dovker/Touchord/img/DSC_5180.jpg

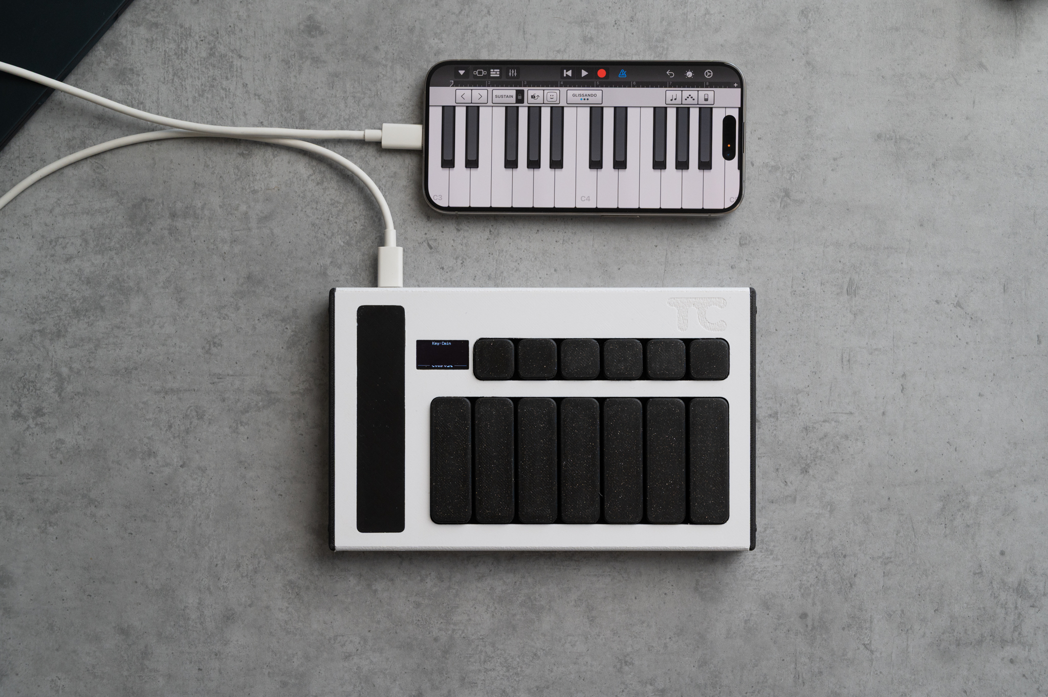
img/DSC_5180.jpg
