dovker/Touchord/img/DSC_5195.jpg

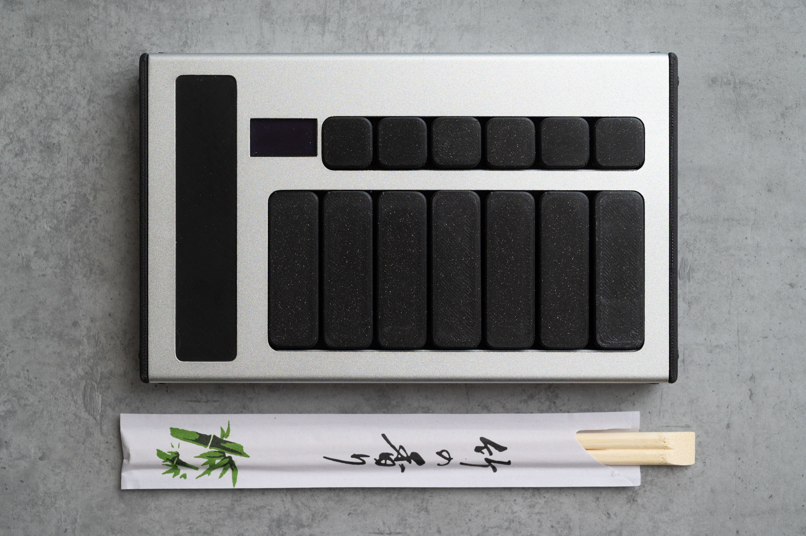
img/DSC_5195.jpg
