dovker/Touchord/src/IO/Midi.c

/*
 * Touchord — MIDI chord controller firmware.
 * Copyright (C) 2025-2026 MB Daugdara
 * SPDX-License-Identifier: GPL-3.0-or-later
 *
 * For more info, email info@daugdara.com
 */

#include "Midi.h"
#include "tusb.h"
#include "hardware/uart.h"

void switch_midi_trs(MidiType type)
{
    //Toggles the TS5A23157DGSR
    switch(type)
    {
        case MIDI_TRS_A:
        gpio_put(MIDI_PIN_IN_1, 0);
        gpio_put(MIDI_PIN_IN_2, 0);
        break;
        case MIDI_TRS_B:
        gpio_put(MIDI_PIN_IN_1, 1);
        gpio_put(MIDI_PIN_IN_2, 1);
        break;
    }
}
void setup_midi_trs(MidiType type)
{
    gpio_init(MIDI_PIN_IN_1);
    gpio_init(MIDI_PIN_IN_2);
    gpio_set_dir(MIDI_PIN_IN_1, GPIO_OUT);
    gpio_set_dir(MIDI_PIN_IN_2, GPIO_OUT);

    switch_midi_trs(type);

    uart_init(uart1, MIDI_BAUD_RATE);
    gpio_set_function(MIDI_PIN_DAT, GPIO_FUNC_UART); //MIDI_PIN_DAT is TX pin
    uart_set_hw_flow(uart1, false, false);
    uart_set_format(uart1, 8, 1, UART_PARITY_NONE);
    uart_set_fifo_enabled(uart1, false);
}

void send_trs_midi(uint8_t* data, uint8_t len)
{
    for(int i = 0; i < len; i++)
    {
        uart_putc_raw(uart1, data[i]);
    }
}

void send_midi_chord(uint8_t channel, uint8_t status, uint8_t* notes, uint8_t length, uint8_t velocity)
{
    for(int i = 0; i < length; i++)
    {
        send_midi_note(channel, status, notes[i], velocity);
    }
}

void send_midi_chord_diff(const uint8_t *prev, const uint8_t *curr,
                          uint8_t channel, uint8_t velocity, bool retrigger)
{
    if (retrigger) {
        for (int i = 0; i < MAX_CHORD; i++)
            if (prev[i]) send_midi_note(channel, NOTE_OFF, prev[i], velocity);
        for (int i = 0; i < MAX_CHORD; i++)
            if (curr[i]) send_midi_note(channel, NOTE_ON,  curr[i], velocity);
        return;
    }
    for (int i = 0; i < MAX_CHORD; i++) {
        uint8_t p = prev[i];
        if (p == 0) continue;
        bool kept = false;
        for (int j = 0; j < MAX_CHORD; j++)
            if (curr[j] == p) { kept = true; break; }
        if (!kept) send_midi_note(channel, NOTE_OFF, p, velocity);
    }
    for (int i = 0; i < MAX_CHORD; i++) {
        uint8_t c = curr[i];
        if (c == 0) continue;
        bool was = false;
        for (int j = 0; j < MAX_CHORD; j++)
            if (prev[j] == c) { was = true; break; }
        if (!was) send_midi_note(channel, NOTE_ON, c, velocity);
    }
}

void send_midi_note(uint8_t channel, uint8_t status, uint8_t note, uint8_t velocity) {
    uint8_t packet[3] = {
        status | (channel & 0x0F),
        note,
        velocity
    };
    tud_midi_stream_write(0, packet, 3);
    send_trs_midi(packet, 3);
}

void send_midi_cc(uint8_t channel, uint8_t cc_num, uint8_t cc_value) {
    uint8_t status = 0xB0 | (channel & 0x0F); 
    uint8_t packet[3] = {
        status,
        cc_num,
        cc_value
    };
    tud_midi_stream_write(0, packet, 3);
    send_trs_midi(packet, 3);
}

void send_poly_aftertouch(uint8_t channel, uint8_t note, uint8_t pressure) {
    uint8_t status = 0xA0 | (channel & 0x0F);

    uint8_t packet[3] = {
        status,
        note,
        pressure
    };
   tud_midi_stream_write(0, packet, 3);
   send_trs_midi(packet, 3);
}

void send_aftertouch(uint8_t channel, uint8_t pressure)
{
    uint8_t status = 0xD0 | (channel & 0x0F);

    uint8_t packet[2] = {
        status,
        pressure
    };
   tud_midi_stream_write(0, packet, 2);
   send_trs_midi(packet, 2);
}
